imo00o/FrostOrtho-3dprint-data/case/v1.2.0/3mf/paw3222.3mf

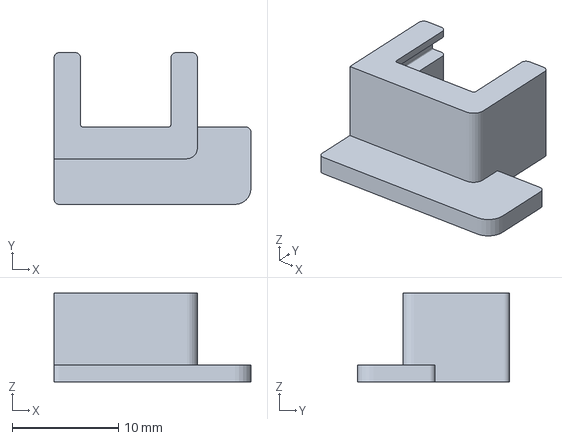
[picture p22: CAD file, 2026-05-10]
case/v1.2.0/3mf/paw3222.3mf
18.6 x 14.3 x 8.36 mm
