imo00o/FrostOrtho-3dprint-data/case/v1.2.0/stl/case_top_L.stl

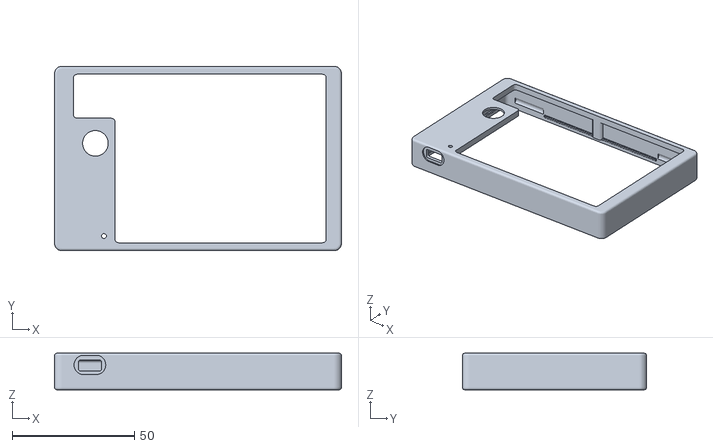
[picture p23: CAD file, 2026-06-25]
case/v1.2.0/stl/case_top_L.stl
117.5 x 75.5 x 15.0
