imo00o/FrostOrtho-3dprint-data/case/v1.2.0/3mf/nob.3mf

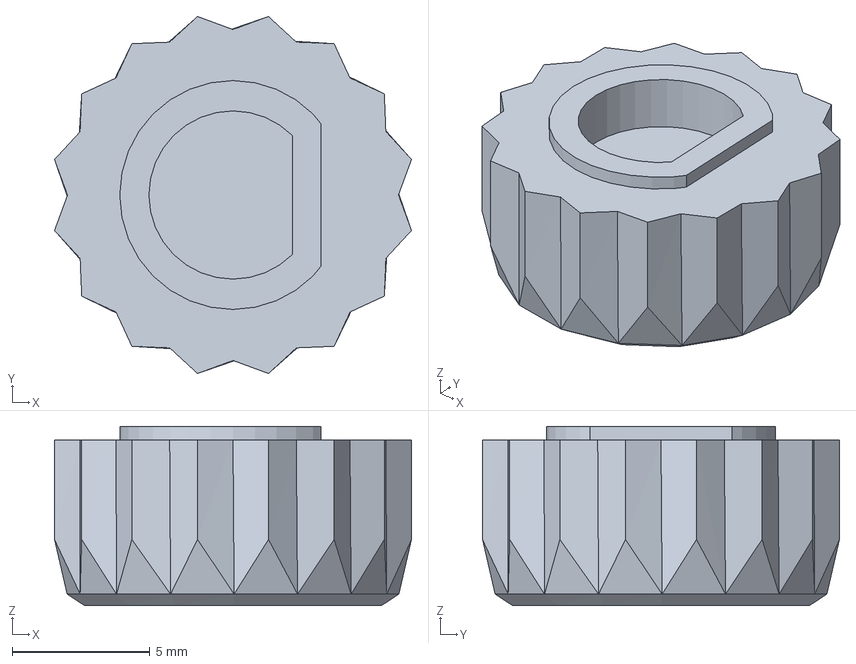
[picture p24: CAD file, 2026-04-24]
case/v1.2.0/3mf/nob.3mf
12.9 x 12.9 x 6.50 mm
